lassiipk/ModuPad/Images/CAD_Images/01_ModuPad_BottomCase_Sketch.png

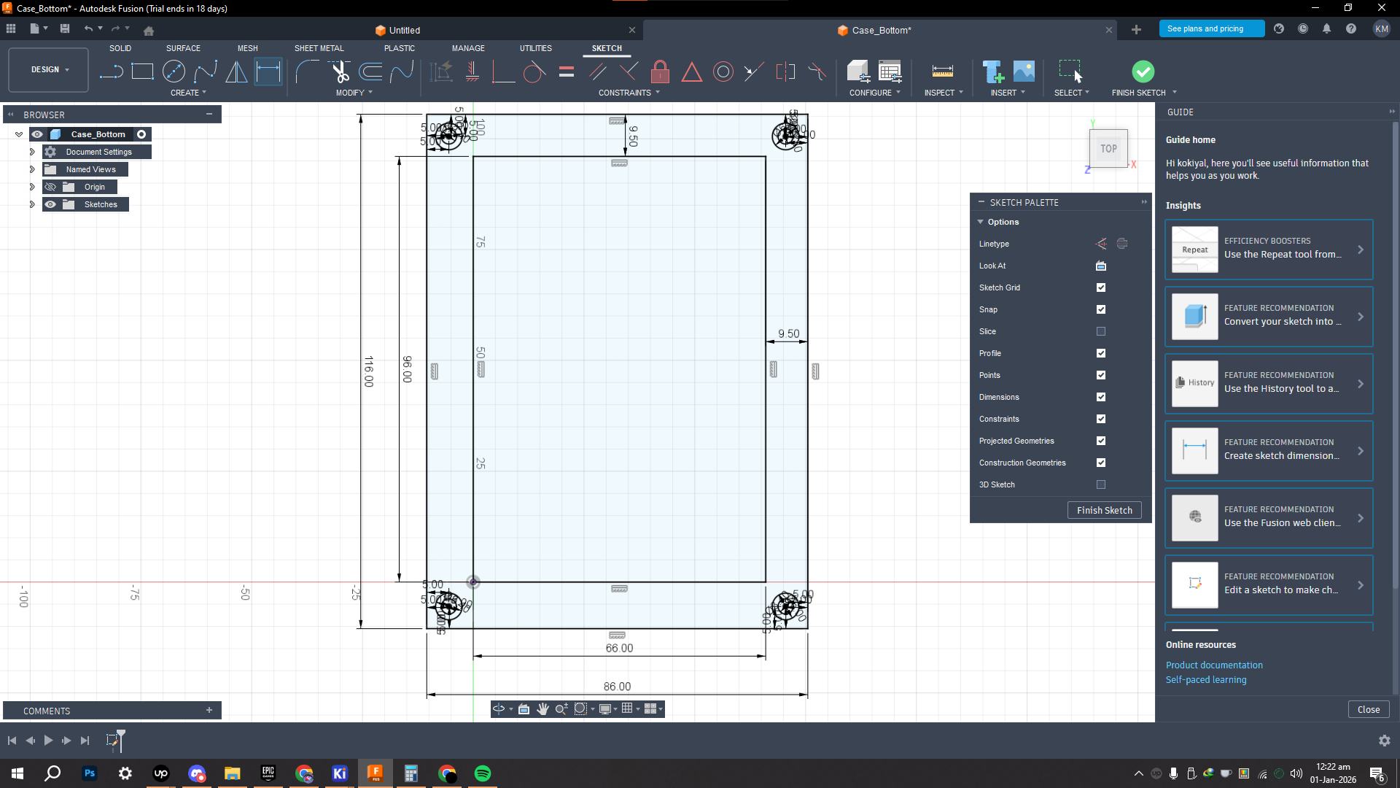
Images/CAD_Images/01_ModuPad_BottomCase_Sketch.png
