lassiipk/ModuPad/Images/CAD_Images/02_ModuPad_UpperCase_Sketch.png

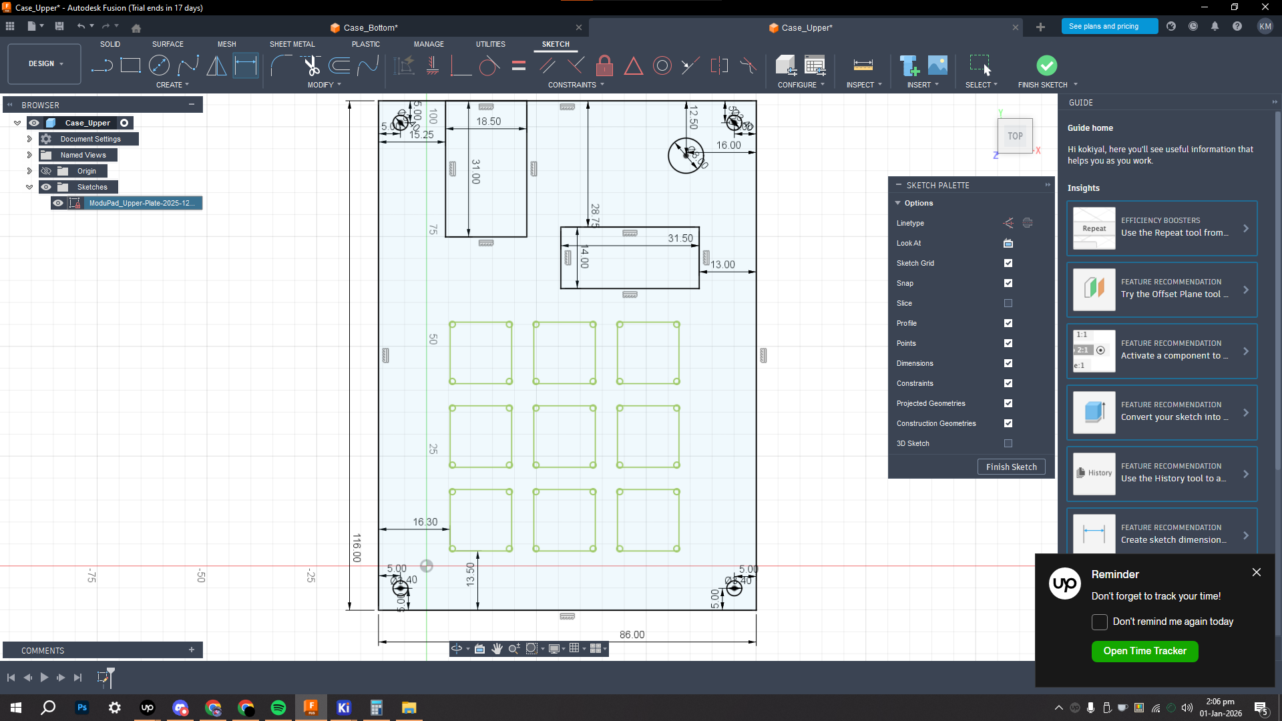
Images/CAD_Images/02_ModuPad_UpperCase_Sketch.png
