lassiipk/ModuPad/Images/CAD_Images/04_ModuPad_UpperCase_ExtrudeDimentions.png

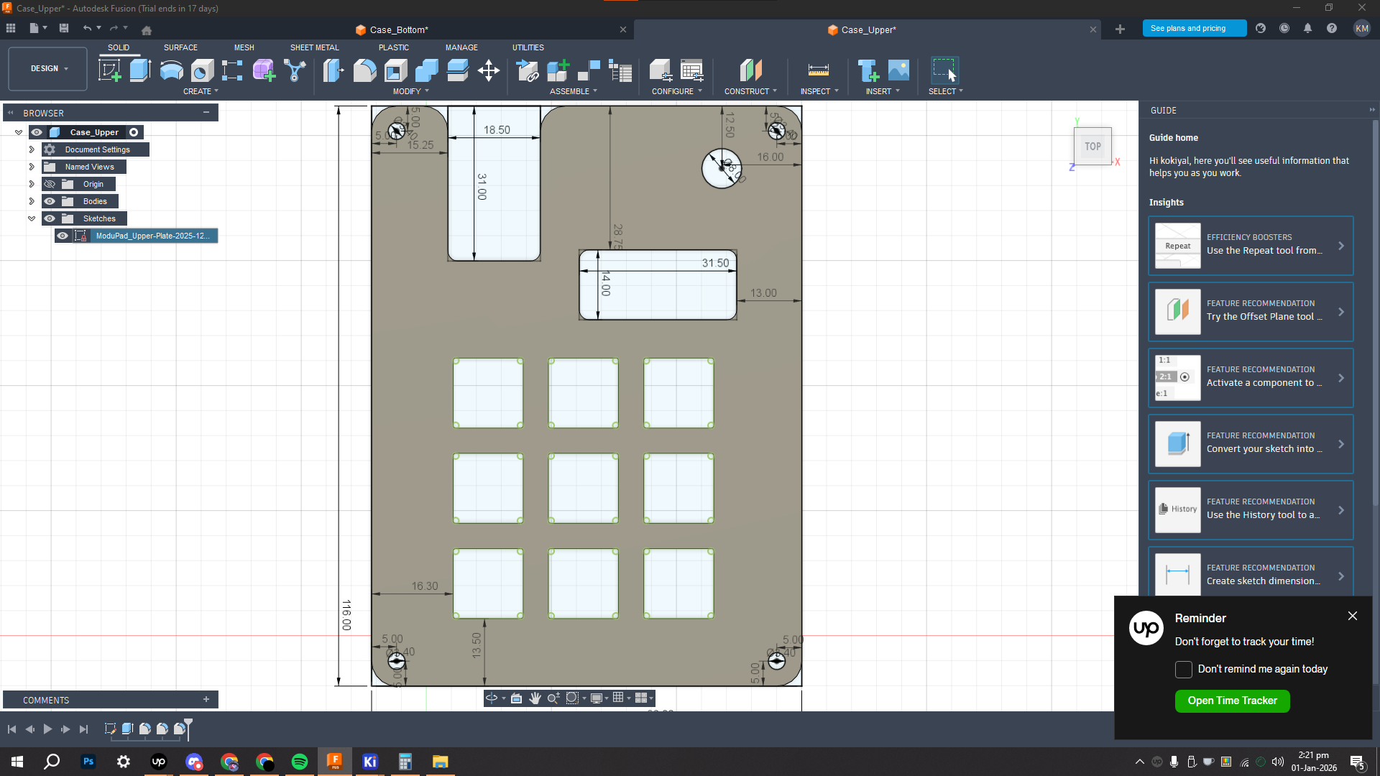
Images/CAD_Images/04_ModuPad_UpperCase_ExtrudeDimentions.png
