lassiipk/ModuPad/Images/CAD_Images/ModuPad_FullProduct_Image.png

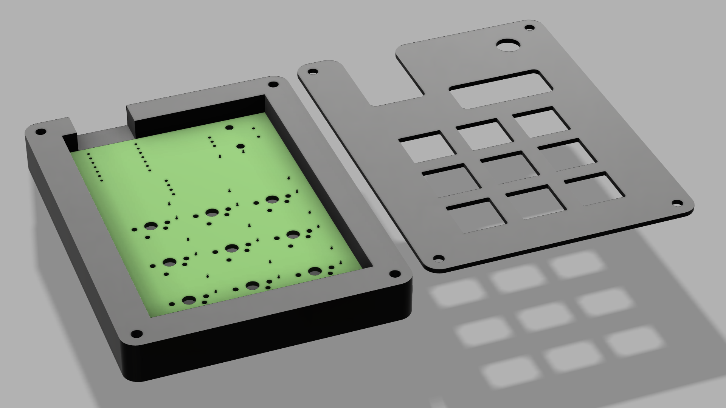
Images/CAD_Images/ModuPad_FullProduct_Image.png
