lassiipk/ModuPad/Images/KiCad_Images/03.0_KiCad_MCU_Dimentions.png

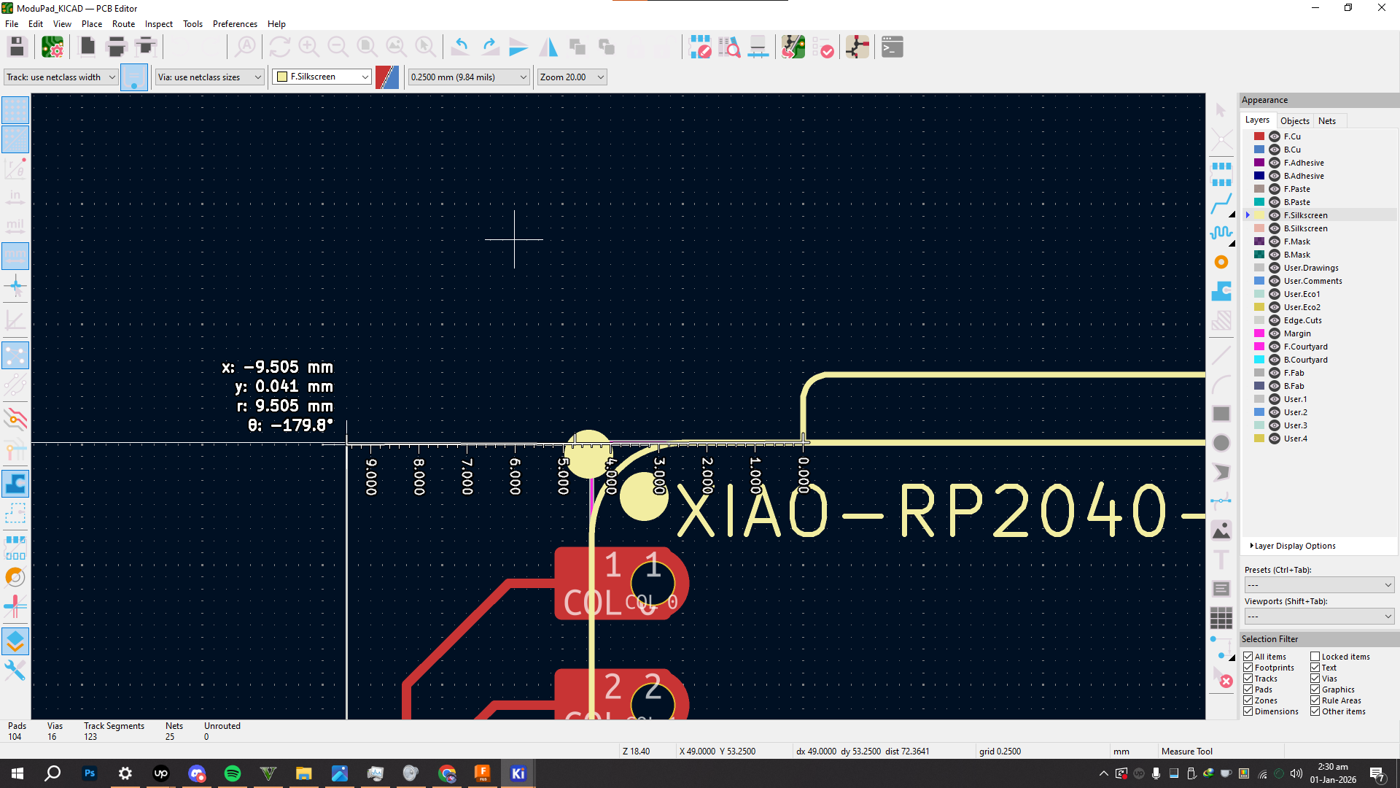
Images/KiCad_Images/03.0_KiCad_MCU_Dimentions.png
