lassiipk/ModuPad/Images/KiCad_Images/04_KiCad_PCB_Dimentions.png

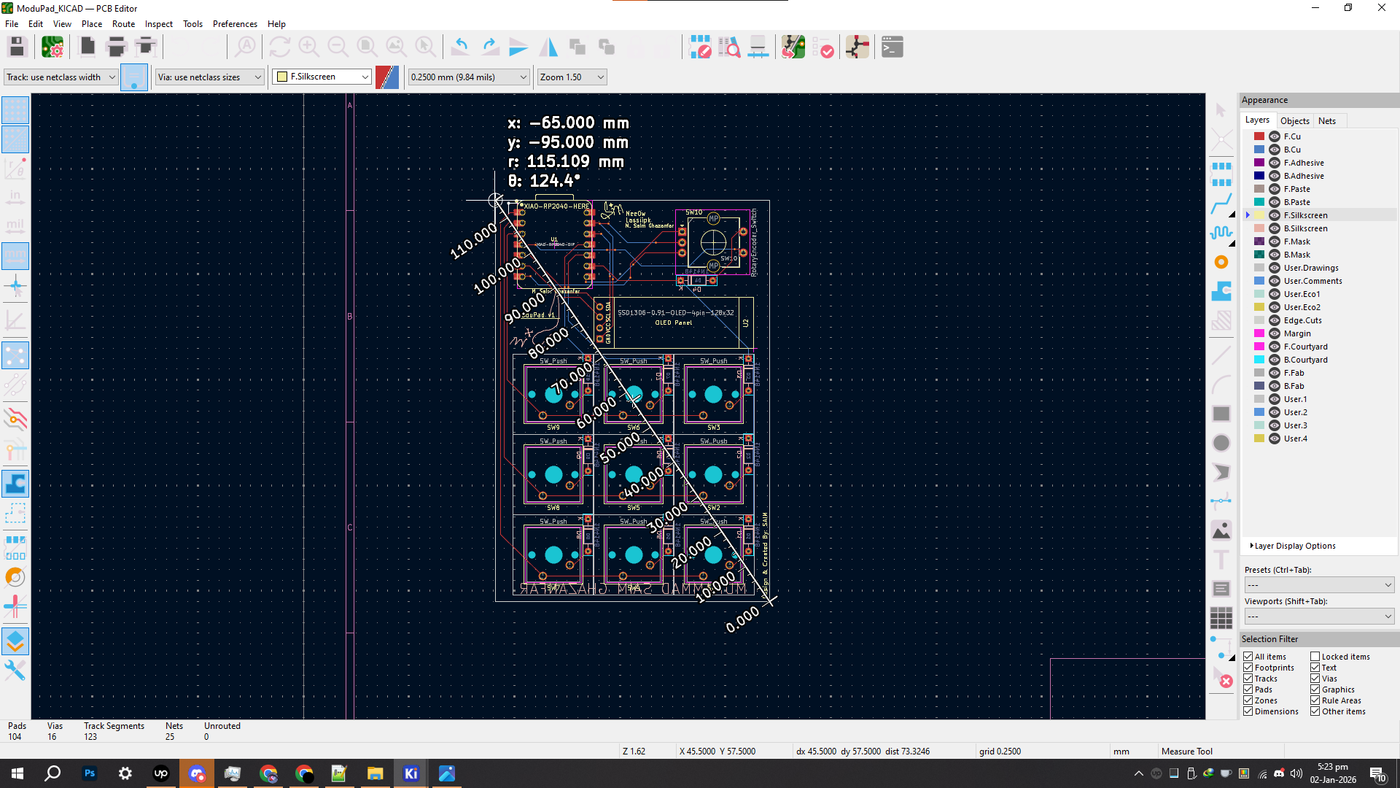
Images/KiCad_Images/04_KiCad_PCB_Dimentions.png
