lassiipk/ModuPad/Images/KiCad_Images/05_KiCad_OLED_Full-Dimentions.png

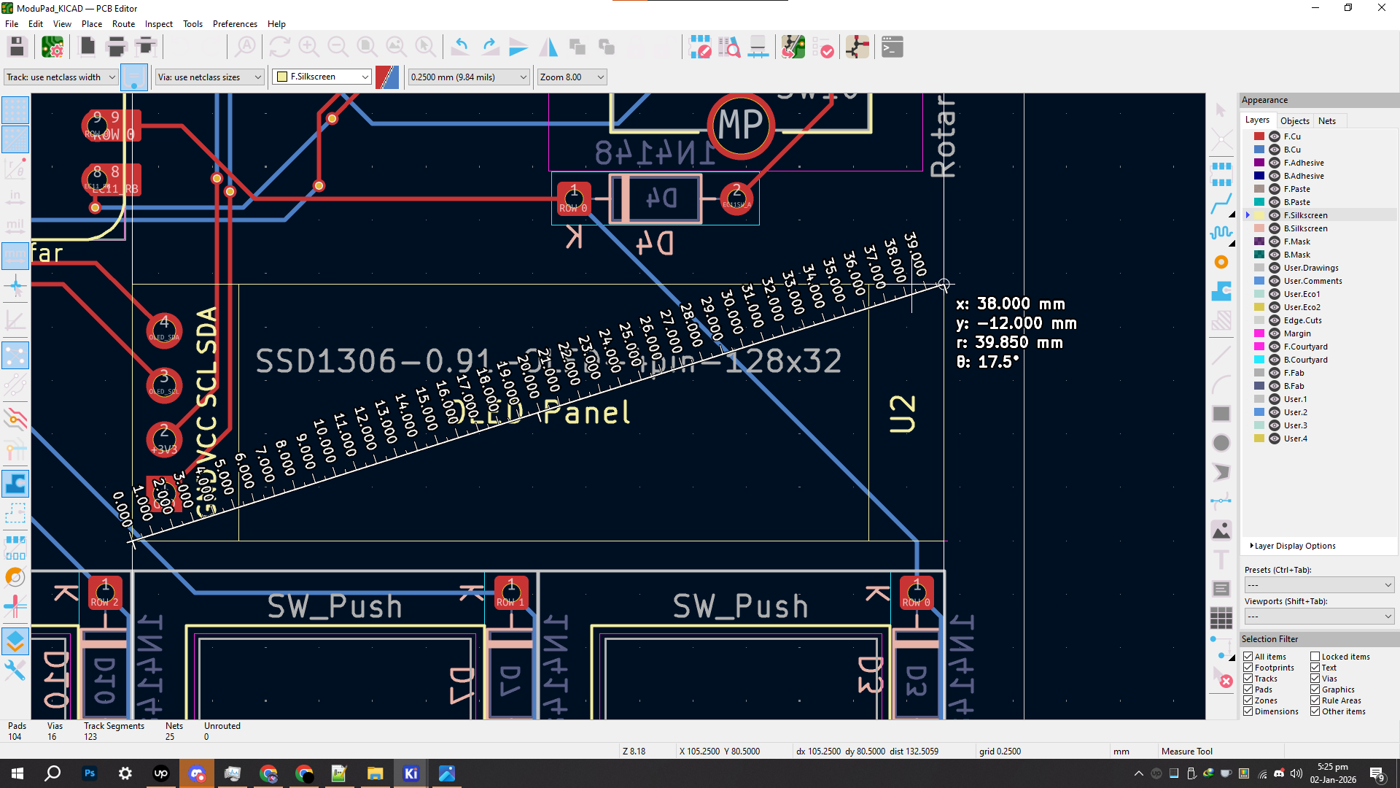
Images/KiCad_Images/05_KiCad_OLED_Full-Dimentions.png
