lassiipk/ModuPad/KiCad Libraries/XIAO Footprints/OPL_Kicad_Library-master/images/XIAO_Family_2.png

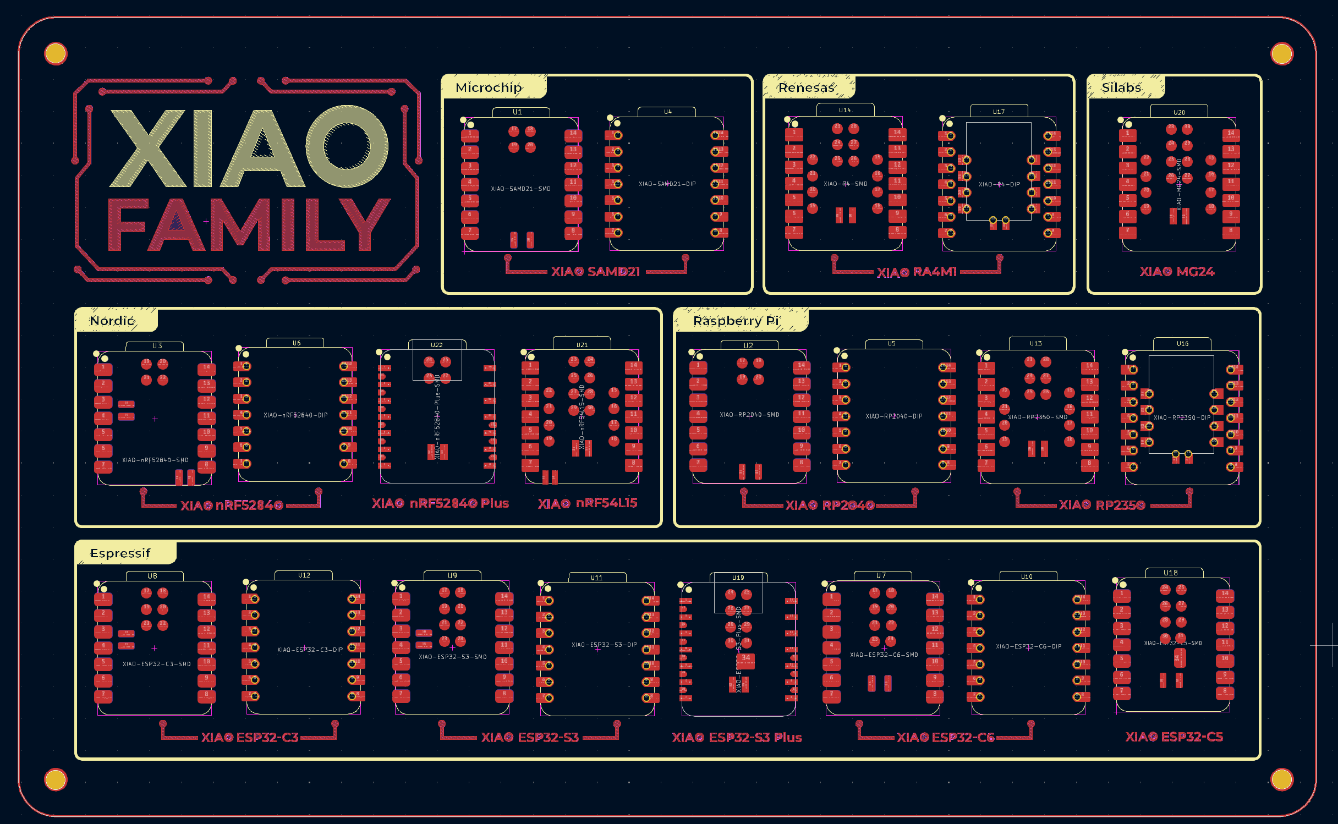
KiCad Libraries/XIAO Footprints/OPL_Kicad_Library-master/images/XIAO_Family_2.png
